semi10/AClock/NewFont.h

// copied from http://heim.ifi.uio.no/haakoh/avr/a
#ifndef NewFont_h
#define NewFont_h

#include <avr/pgmspace.h>                // Enable data to be stored in Flash Mem as well as SRAM  

unsigned const char PROGMEM Font[96][5] = {
/*00*/ {0x00, 0x00, 0x00, 0x00, 0x00}, // space
/*01*/ {0x00, 0x00, 0xfa, 0x00, 0x00}, // !
/*02*/ {0x00, 0x20, 0x40, 0x20, 0x40}, // "
/*03*/ {0x14, 0x3e, 0x14, 0x3e, 0x14}, // #
/*04*/ {0x62, 0x92, 0xfe, 0x92, 0x8c}, // $
/*05*/ {0x66, 0x6c, 0x18, 0x36, 0x66}, // %
/*06*/ {0x5c, 0xa2, 0xb6, 0x48, 0x14}, // &
/*07*/ {0x00, 0x00, 0xe0, 0x00, 0x00}, // '
/*08*/ {0x00, 0x00, 0x00, 0x38, 0xc6}, // (
/*09*/ {0xc6, 0x38, 0x00, 0x00, 0x00}, // )
/*10*/ {0x44, 0x28, 0x7c, 0x28, 0x44}, // *
/*11*/ {0x10, 0x10, 0x7c, 0x10, 0x10}, // +
/*12*/ {0x02, 0x04, 0x00, 0x00, 0x00}, // ,
/*13*/ {0x10, 0x10, 0x10, 0x10, 0x10}, // - 
/*14*/ {0x02, 0x00, 0x00, 0x00, 0x00}, // .
/*15*/ {0x02, 0x0c, 0x10, 0x60, 0x80}, // /
  
/*16*/ {0x7c, 0x8a, 0x92, 0xa2, 0x7c}, // 0 
/*17*/ {0x00, 0x42, 0xfe, 0x02, 0x00}, // 1
/*18*/ {0x42, 0x86, 0x8a, 0x92, 0x62}, // 2
/*19*/ {0x44, 0x82, 0x92, 0x92, 0x6c}, // 3 
/*20*/ {0x18, 0x28, 0x48, 0xfe, 0x08}, // 4
/*21*/ {0xe4, 0xa2, 0xa2, 0xa2, 0x9c}, // 5
/*22*/ {0x7c, 0x92, 0x92, 0x92, 0x4c}, // 6
/*23*/ {0x80, 0x80, 0x9e, 0xa0, 0xc0}, // 7
/*24*/ {0x6c, 0x92, 0x92, 0x92, 0x6c}, // 8
/*25*/ {0x64, 0x92, 0x92, 0x92, 0x7c}, // 9
  
/*26*/ {0x28, 0x00, 0x00, 0x00, 0x00}, // :
/*27*/ {0x02, 0x24, 0x00, 0x00, 0x00}, // ;
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
/*90*/ {0x22, 0x32, 0x2a, 0x26, 0x22}, // z
/*91*/ {0x00, 0x00, 0x10, 0x6c, 0x82}, // {
/*92*/ {0x00, 0x00, 0xfe, 0x00, 0x00}, // |
/*93*/ {0x82, 0x6c, 0x10, 0x00, 0x00}, // }
/*94*/ {0x10, 0x10, 0x54, 0x38, 0x10}, // ->
/*95*/ {0x10, 0x38, 0x54, 0x10, 0x10}  // <-
   
};
#endif
